yorkmodular-cc/bad-trip-vco/images/il_794xN.1995096573_qt7h.jpg

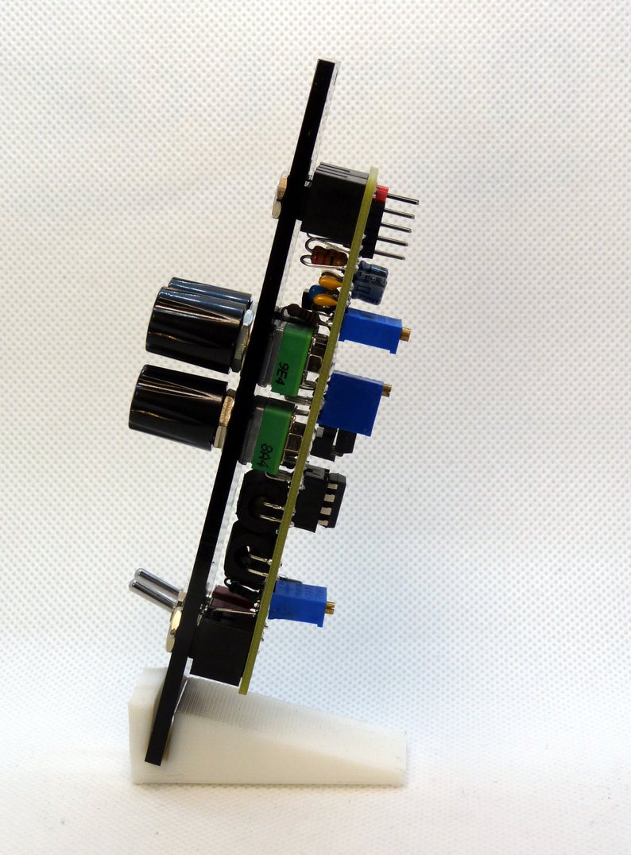
images/il_794xN.1995096573_qt7h.jpg
